Ansuzalgiz/Falcon/Images/Flywheels1.jpg

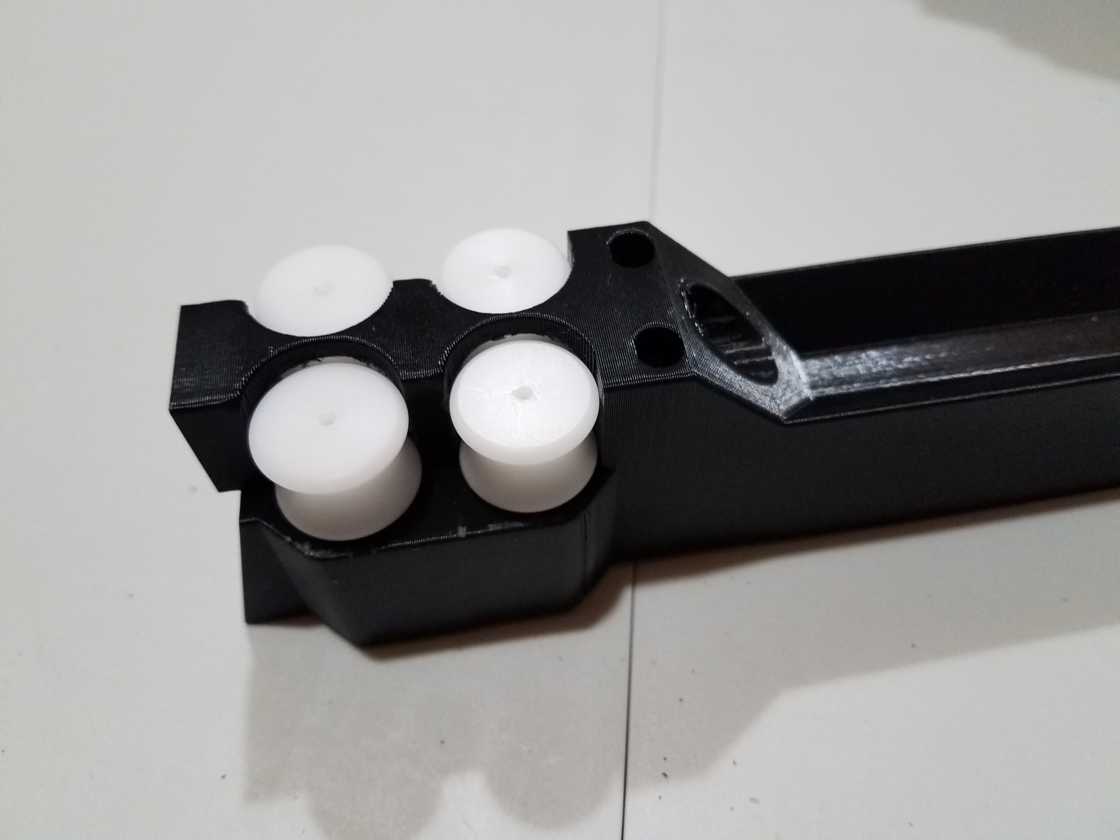
Images/Flywheels1.jpg
