Ansuzalgiz/Falcon/Images/HOLDsterCover.jpg

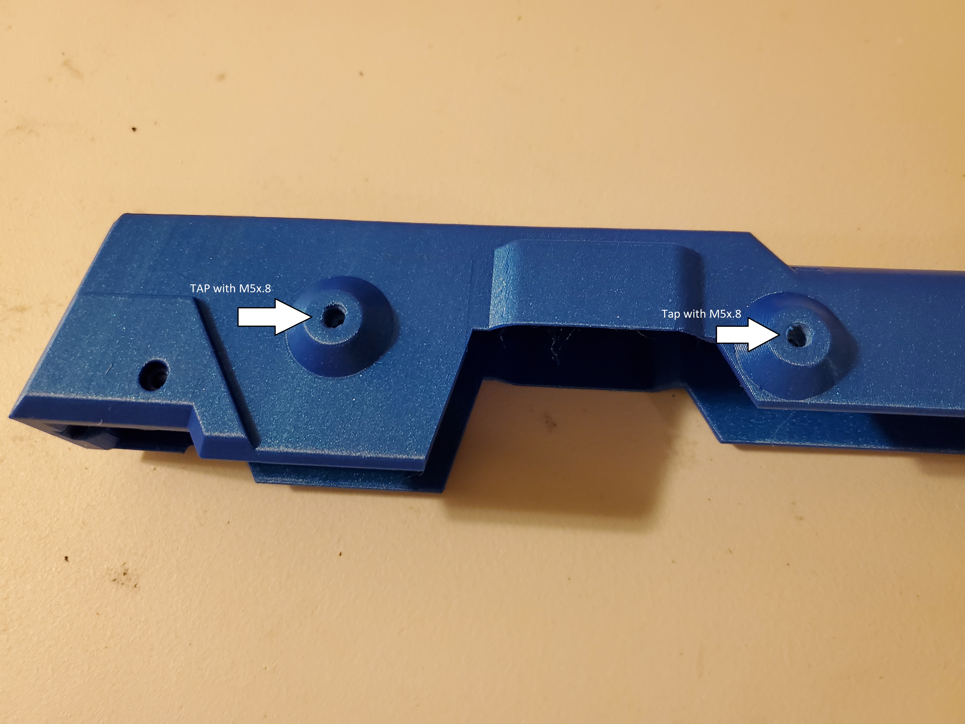
Images/HOLDsterCover.jpg
