Ansuzalgiz/Falcon/Images/HOLDsterFinished.jpg

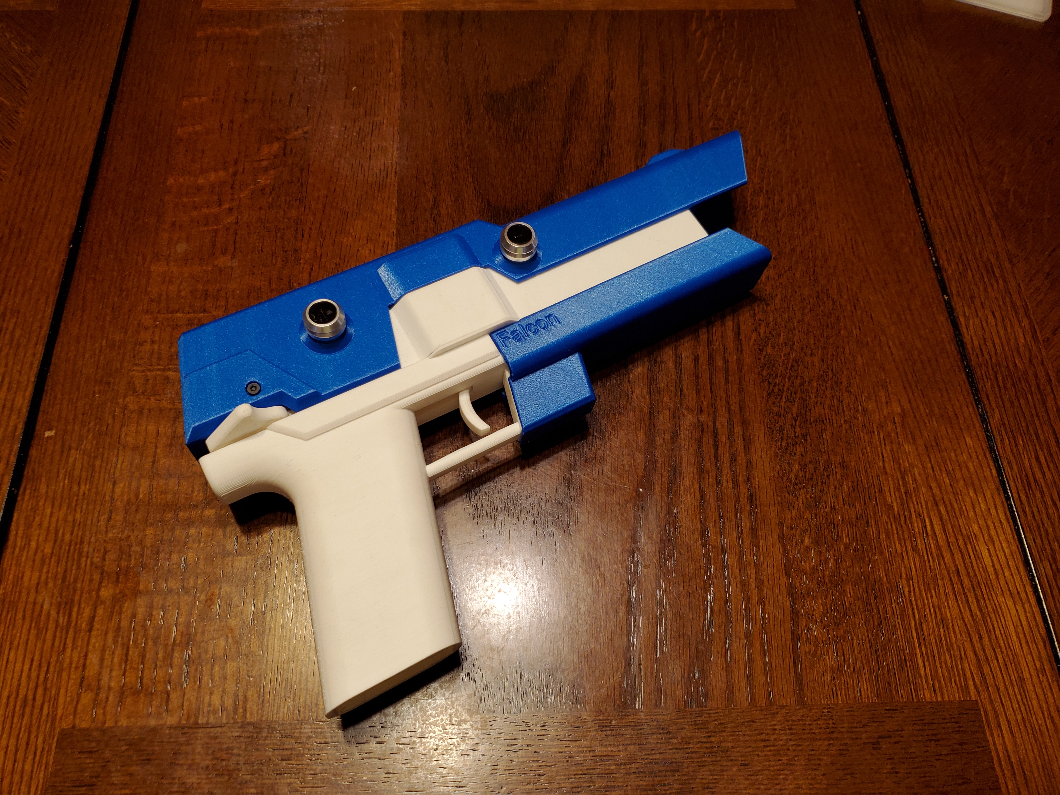
Images/HOLDsterFinished.jpg
