Ansuzalgiz/Falcon/Images/Insert1.jpg

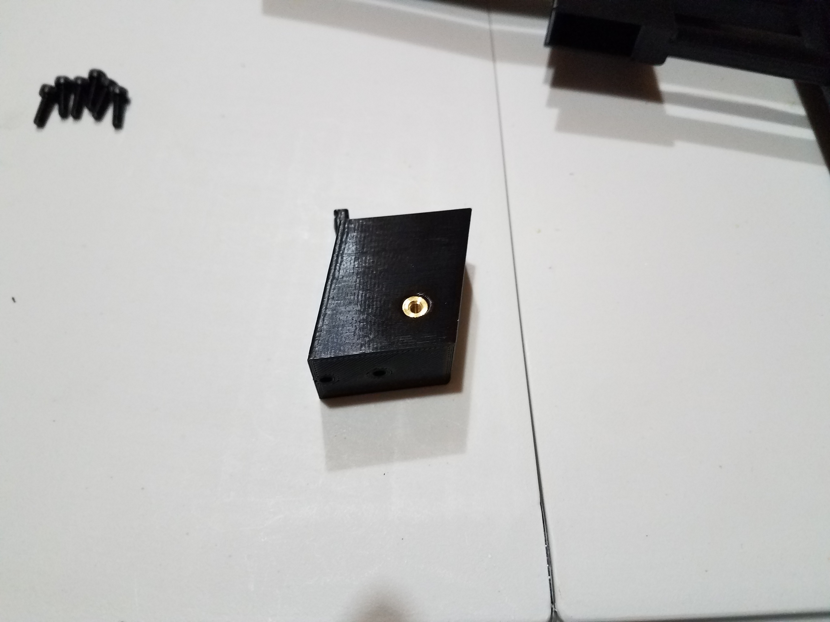
Images/Insert1.jpg
