Ansuzalgiz/Falcon/Images/Insert2.jpg

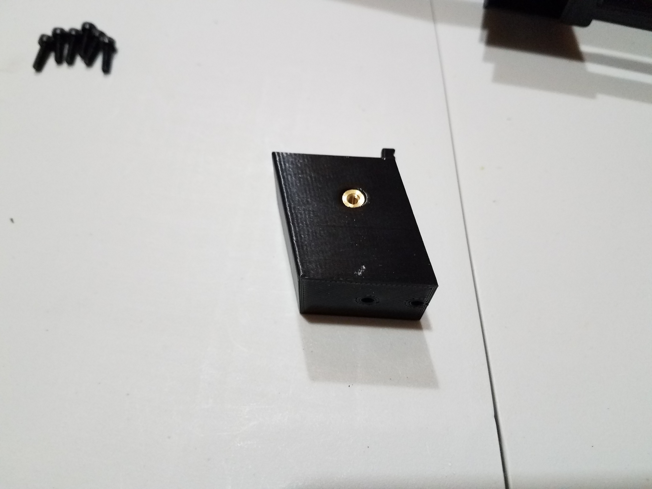
Images/Insert2.jpg
