Ansuzalgiz/Falcon/Images/Insert3.jpg

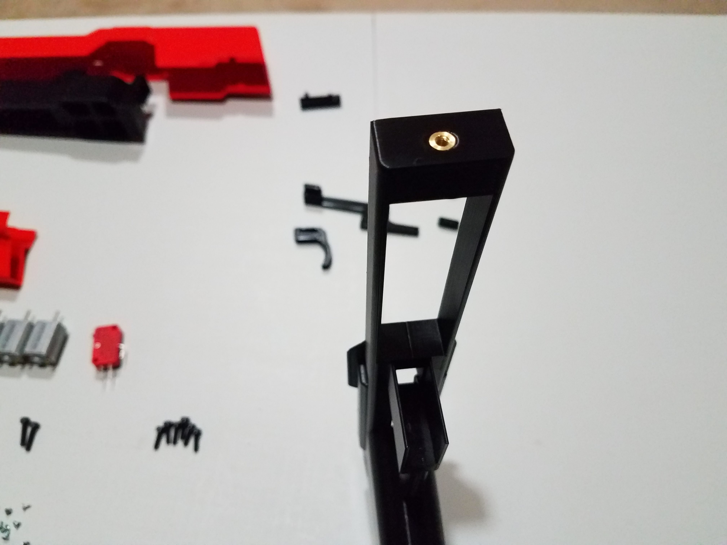
Images/Insert3.jpg
