Ansuzalgiz/Falcon/Images/Insert4.jpg

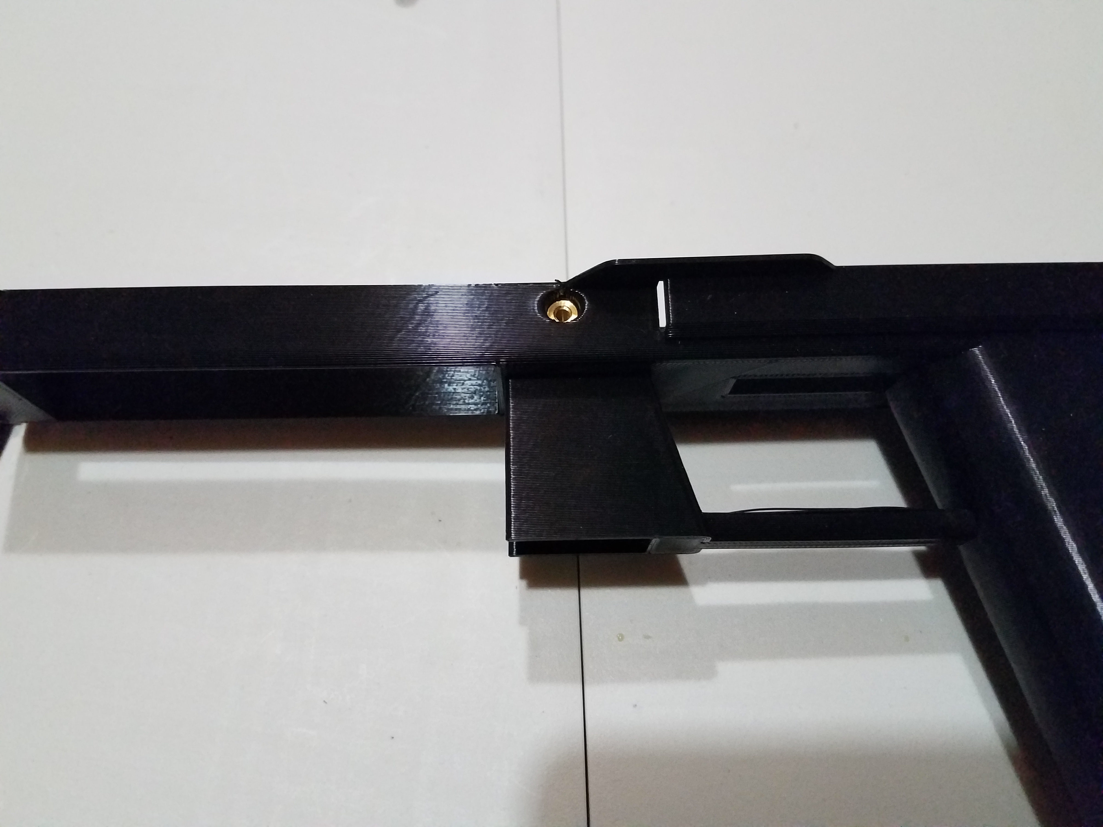
Images/Insert4.jpg
