Ansuzalgiz/Falcon/Images/Insert5.jpg

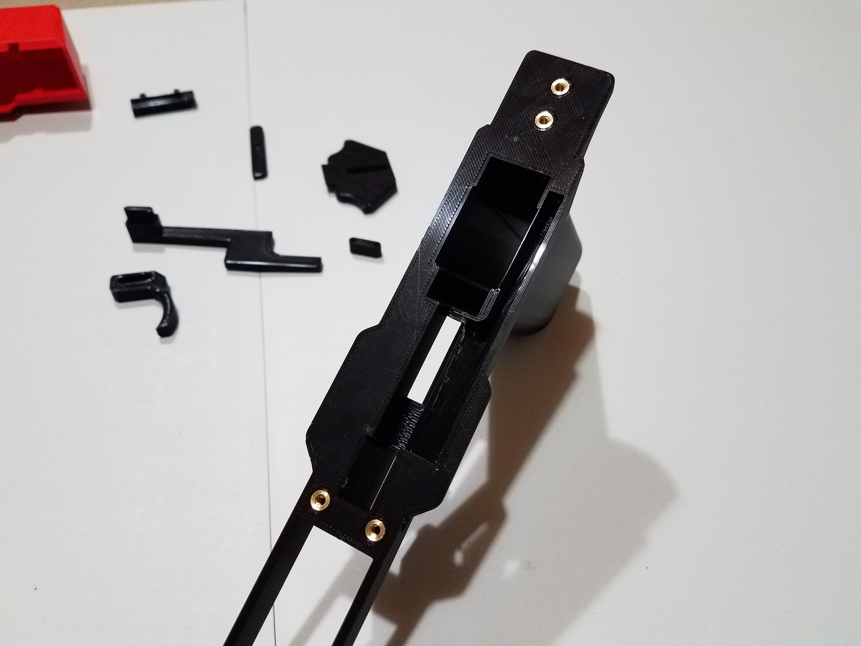
Images/Insert5.jpg
