Ansuzalgiz/Falcon/Images/MagRelease1.jpg

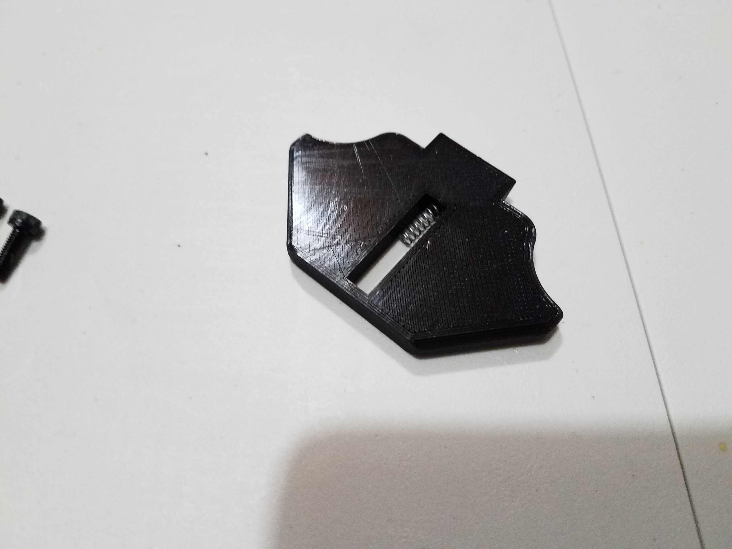
Images/MagRelease1.jpg
