Ansuzalgiz/Falcon/Images/MagRelease2.jpg

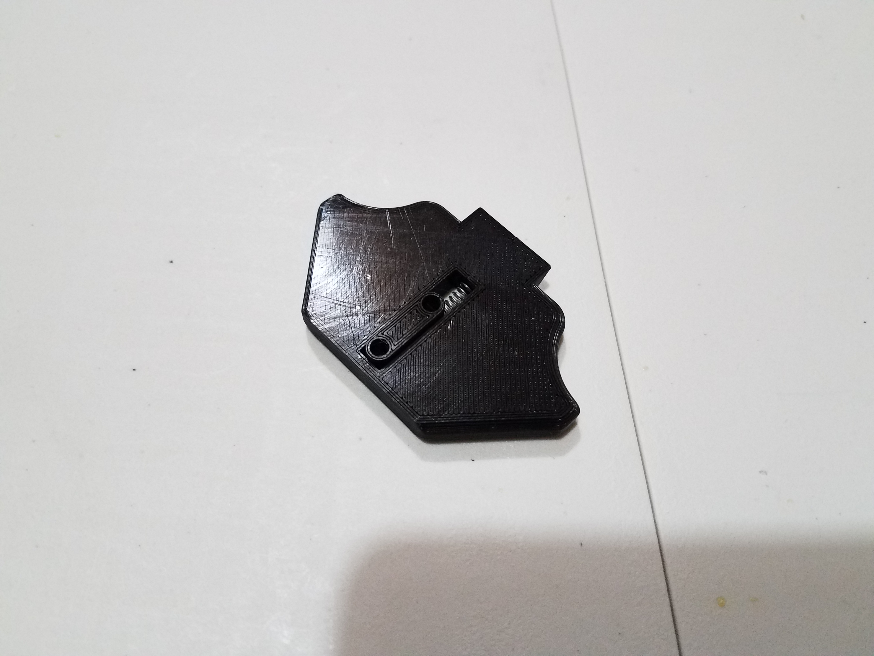
Images/MagRelease2.jpg
