Ansuzalgiz/Falcon/Images/MagRelease3.jpg

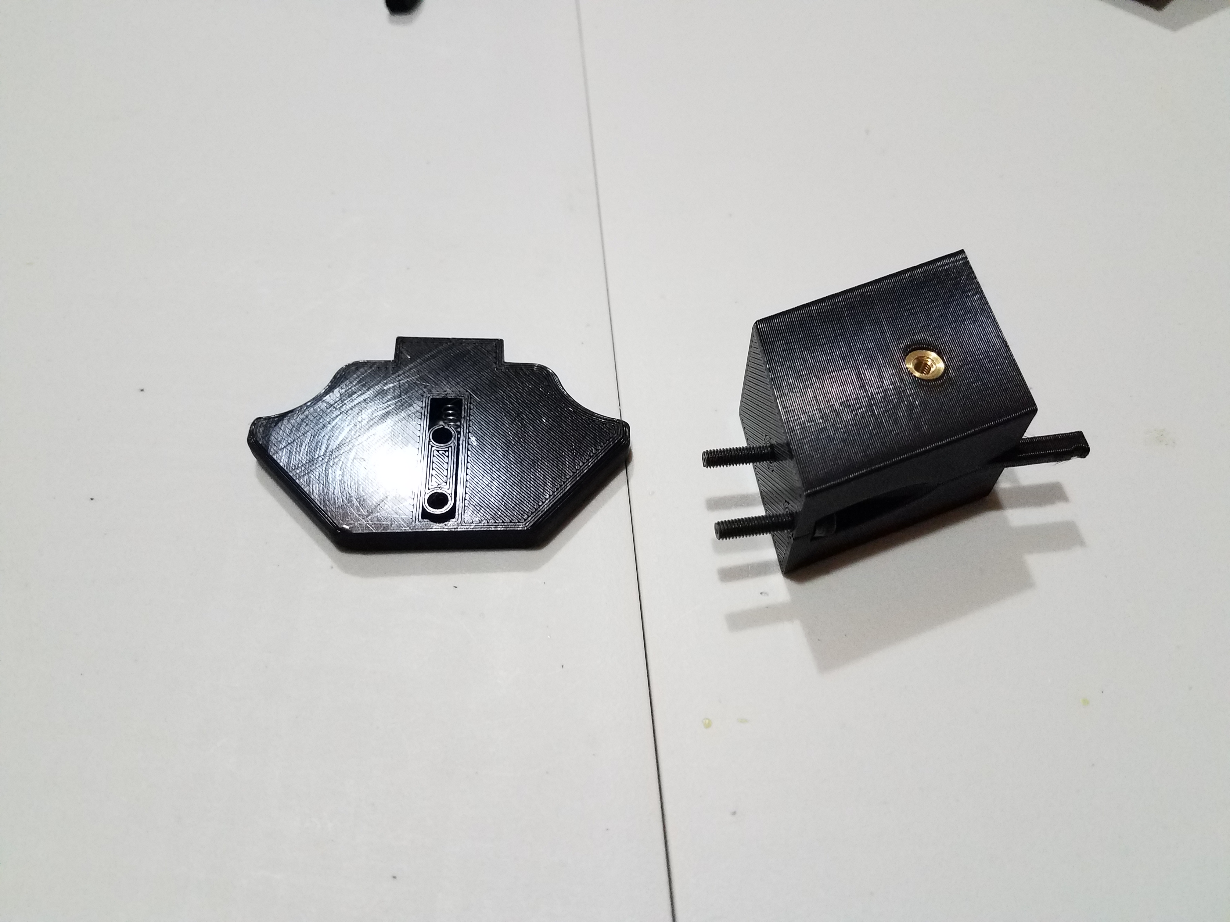
Images/MagRelease3.jpg
