Ansuzalgiz/Falcon/Images/MagRelease4.jpg

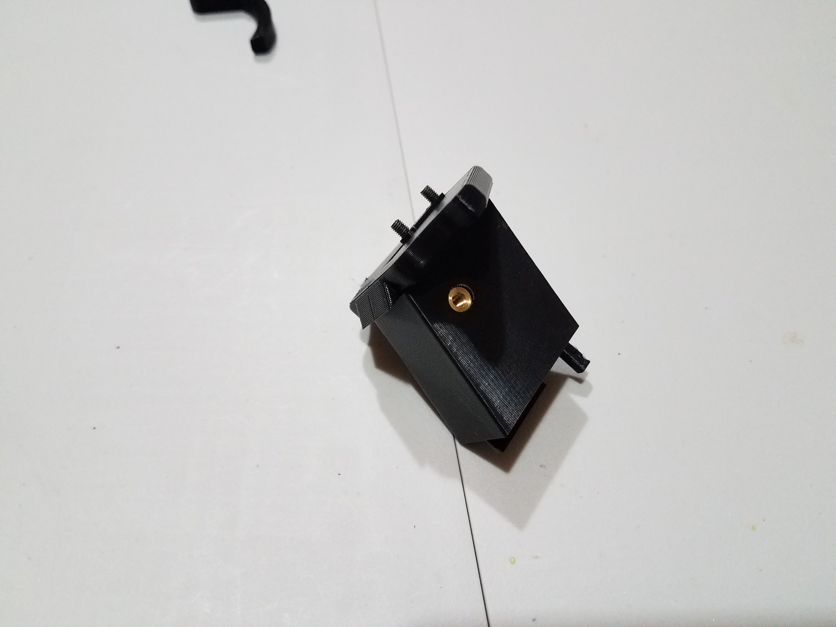
Images/MagRelease4.jpg
