Ansuzalgiz/Falcon/Images/MagRelease5.jpg

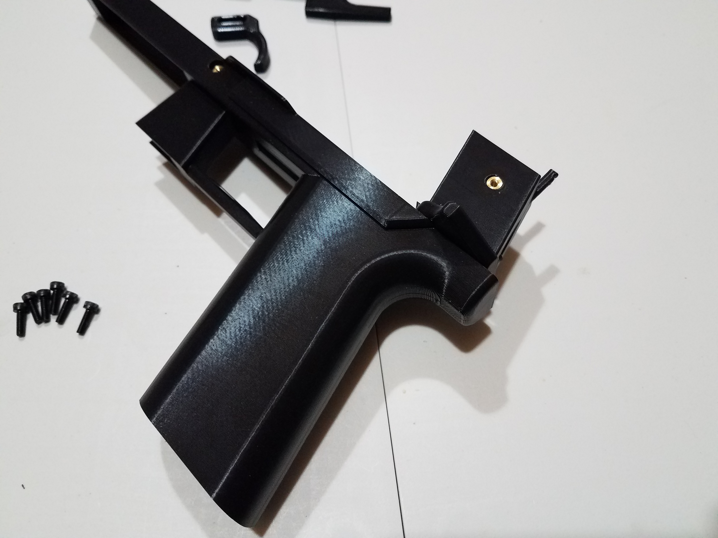
Images/MagRelease5.jpg
