Ansuzalgiz/Falcon/Images/Pusher1.jpg

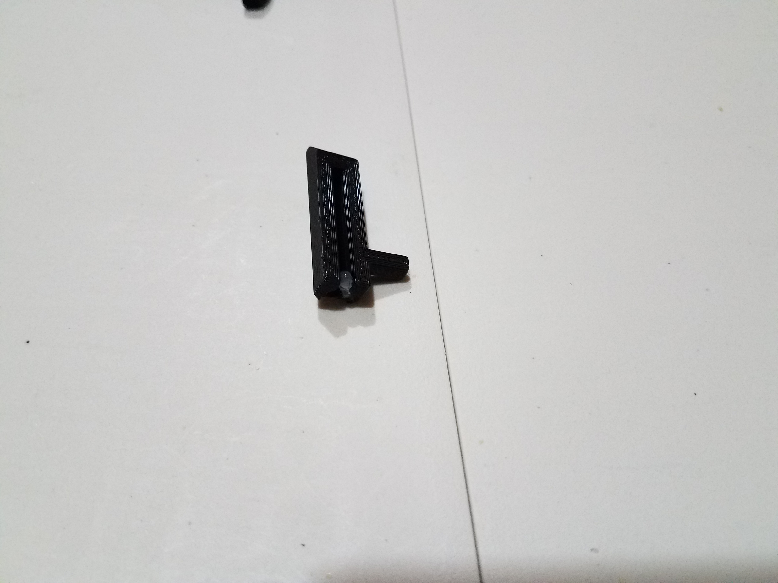
Images/Pusher1.jpg
