Ansuzalgiz/Falcon/Images/Switch1.jpg

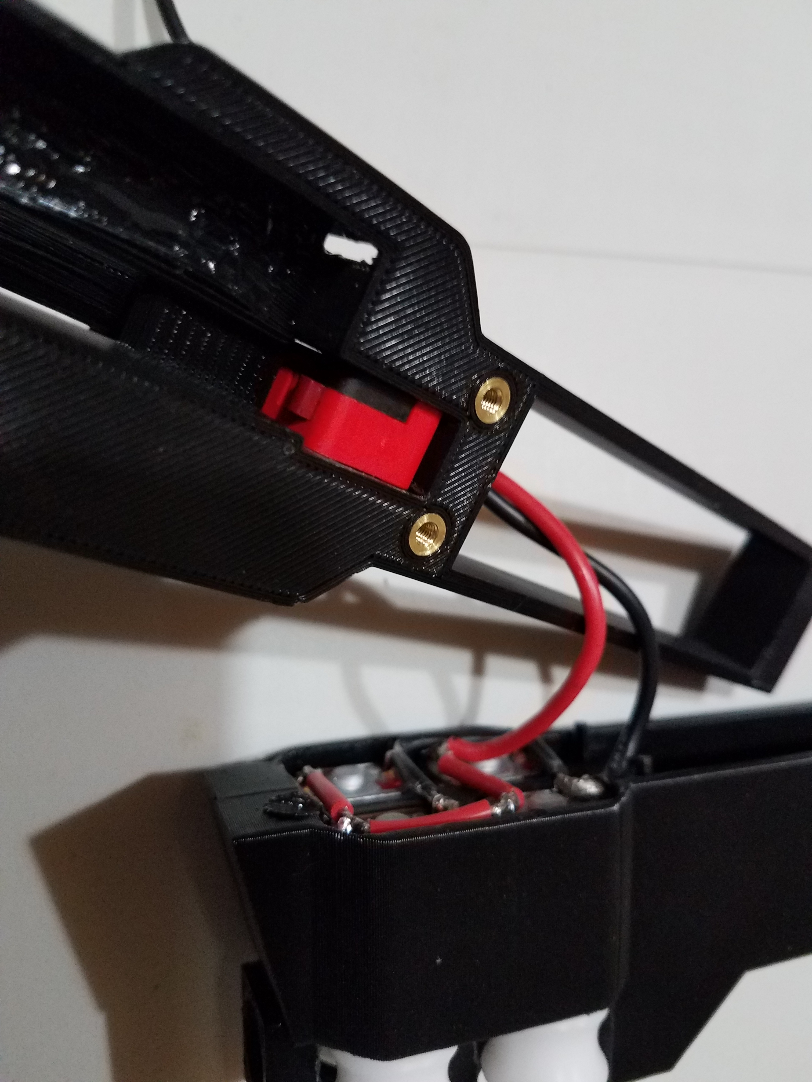
Images/Switch1.jpg
