Ansuzalgiz/Falcon/Images/Trigger1.jpg

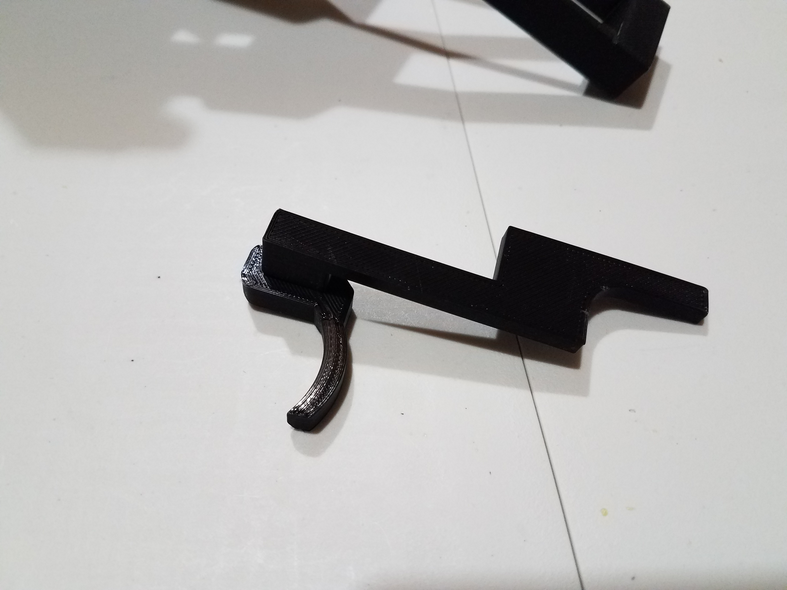
Images/Trigger1.jpg
