Ansuzalgiz/Falcon/Images/Trigger2.jpg

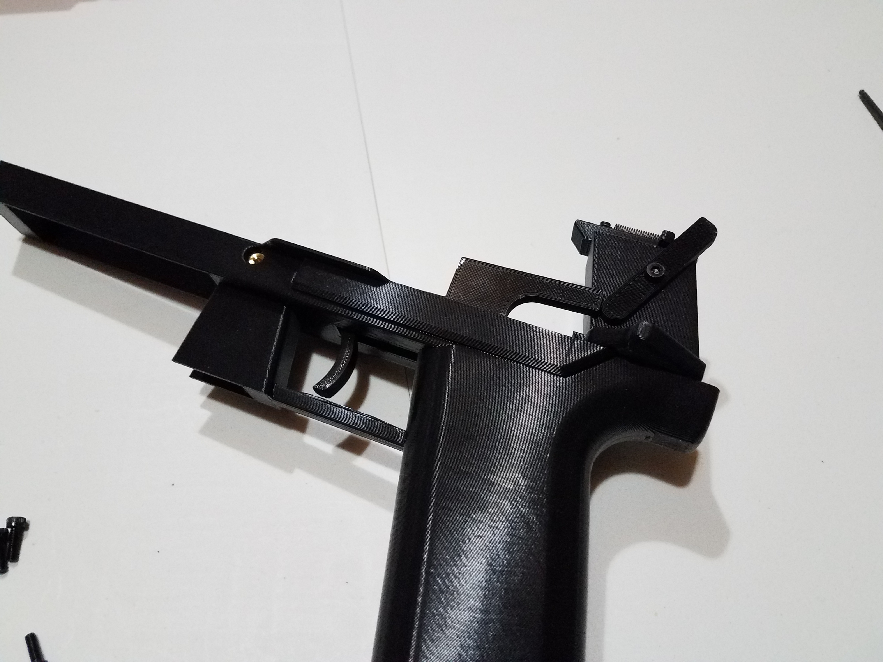
Images/Trigger2.jpg
