Ansuzalgiz/Falcon/Images/KitParts.jpg

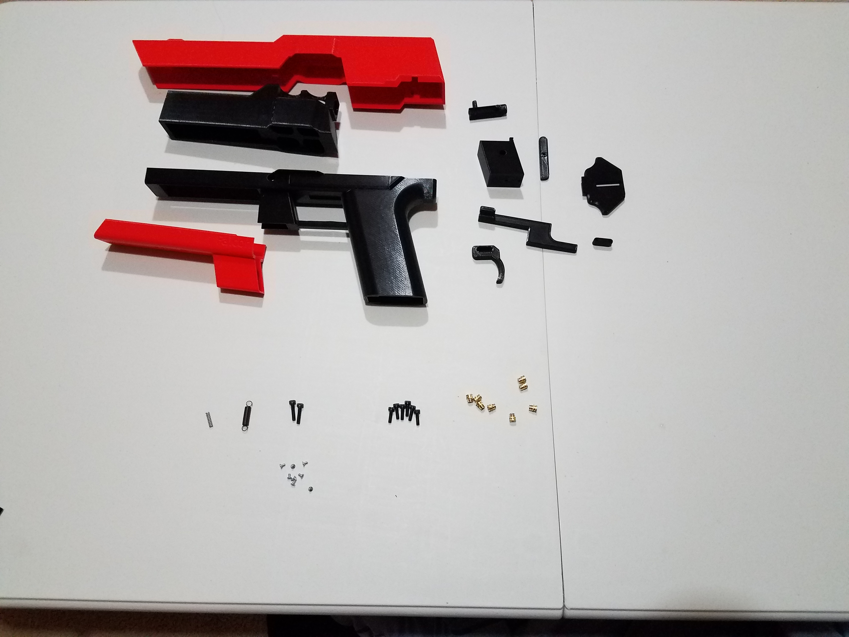
Images/KitParts.jpg
