Ansuzalgiz/Falcon/STLs/BatteryCover.stl

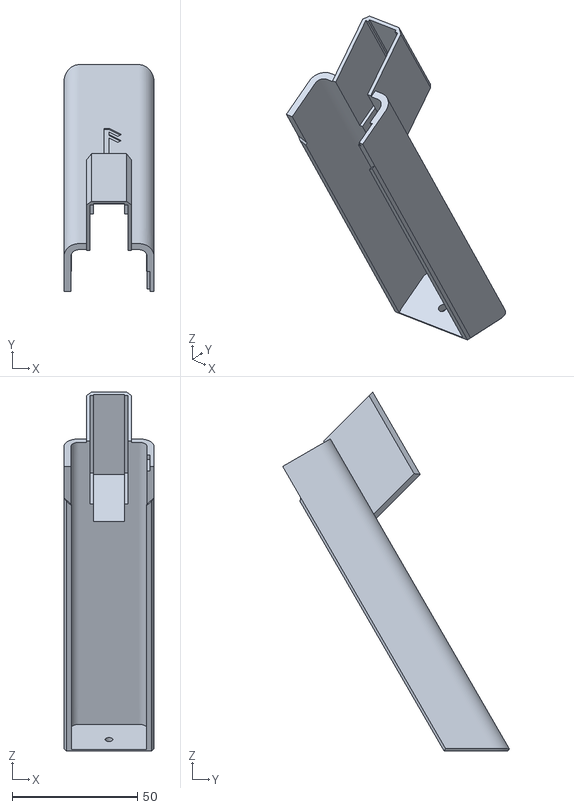
[picture p39: CAD file, 2020-02-27]
STLs/BatteryCover.stl
36.0 x 90.5 x 143.3
