Ansuzalgiz/Falcon/STLs/FlaredMagwell.stl

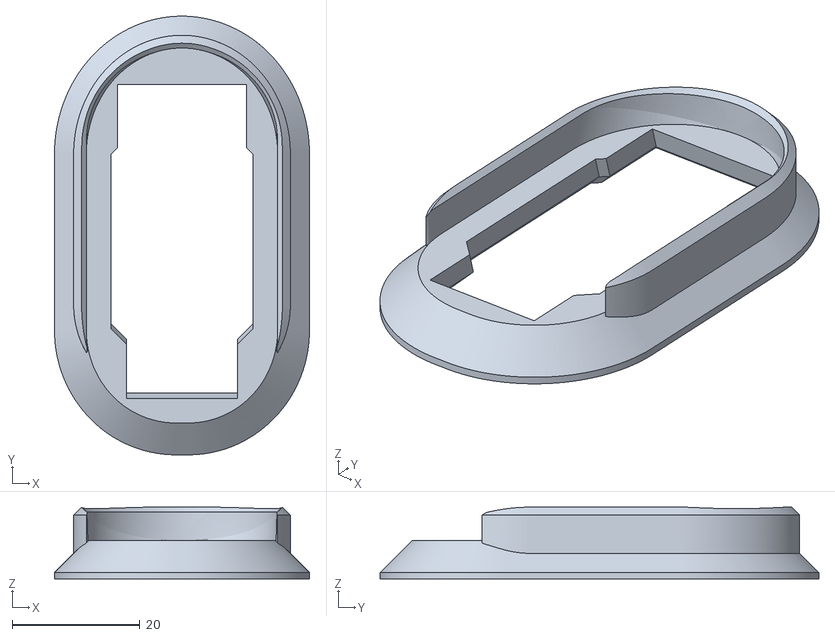
[picture p40: CAD file, 2020-02-27]
STLs/FlaredMagwell.stl
40.0 x 68.8 x 11.3
