Ansuzalgiz/Falcon/STLs/PusherMount.stl

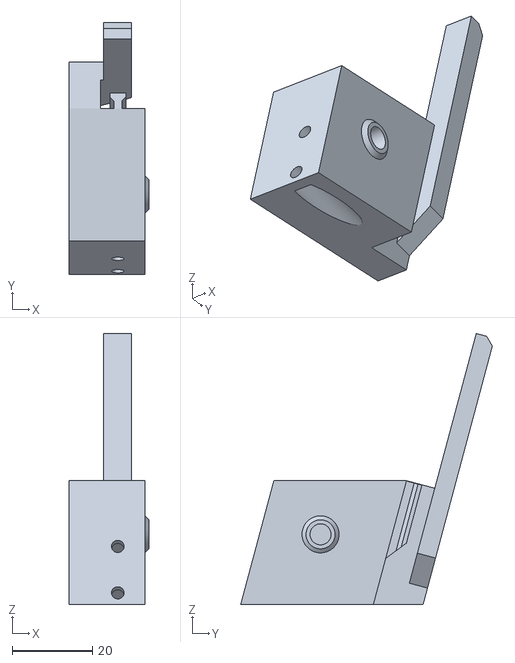
[picture p41: CAD file, 2020-02-27]
STLs/PusherMount.stl
20.0 x 62.8 x 67.7
