Ansuzalgiz/Falcon/Images/FinalAssembly1.jpg

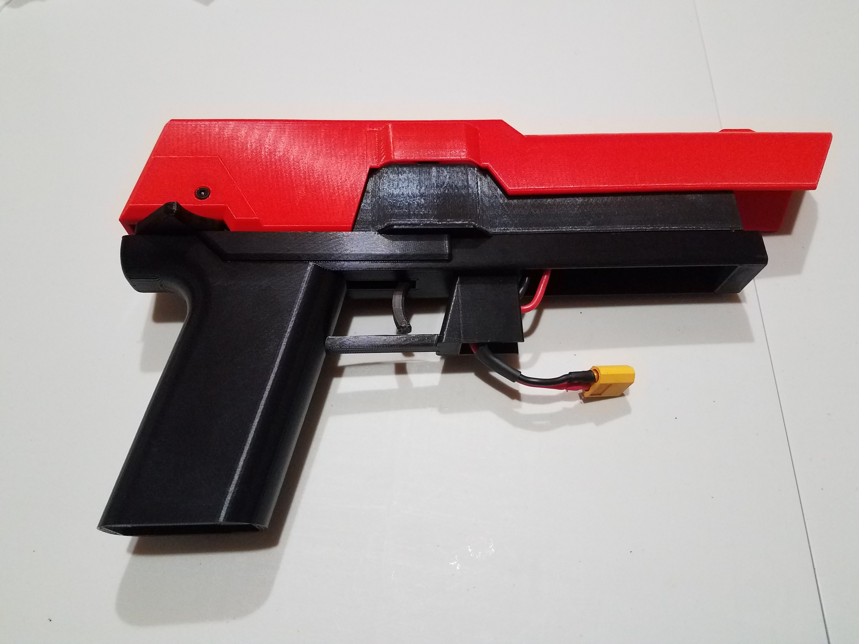
Images/FinalAssembly1.jpg
