Ansuzalgiz/Falcon/Images/FinalAssembly2.jpg

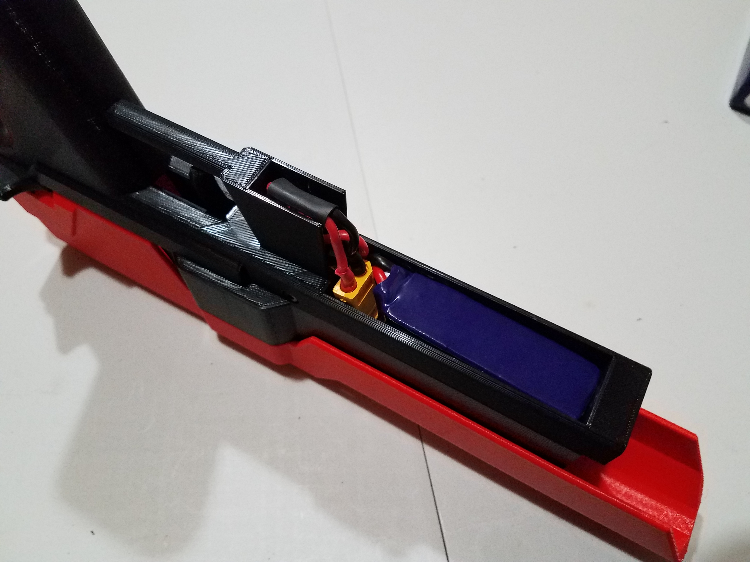
Images/FinalAssembly2.jpg
