Ansuzalgiz/Falcon/Images/FinalAssembly3.jpg

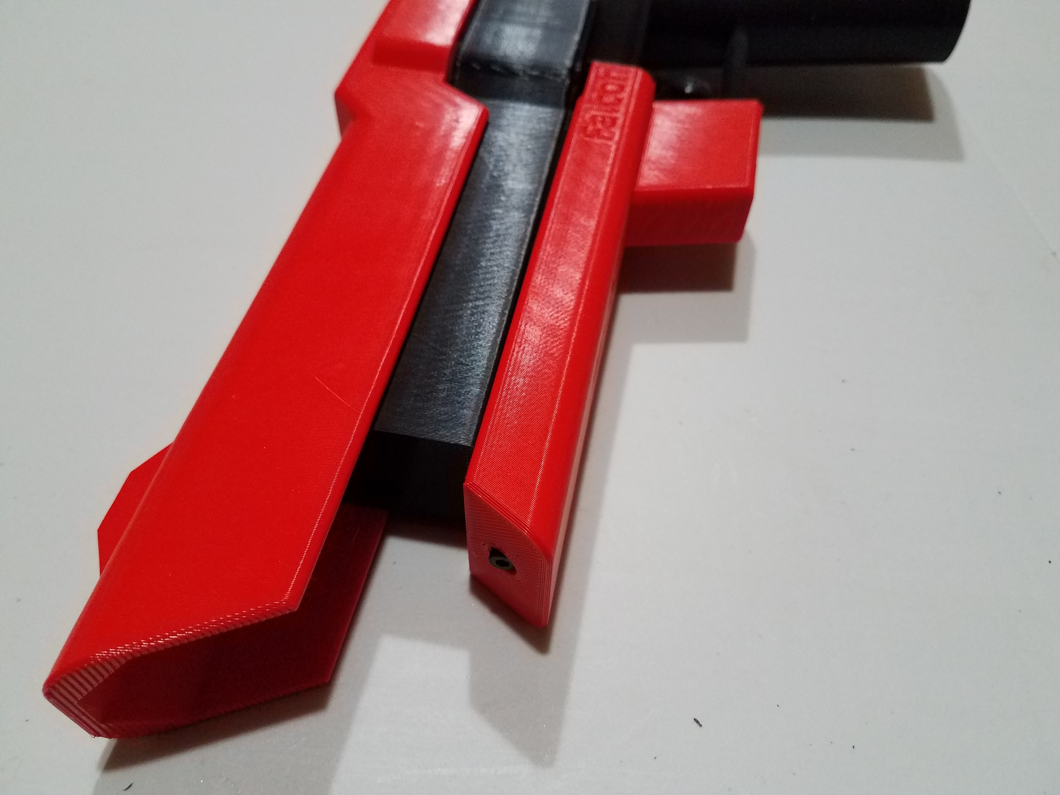
Images/FinalAssembly3.jpg
