Ansuzalgiz/Falcon/Images/Wiring2.jpg

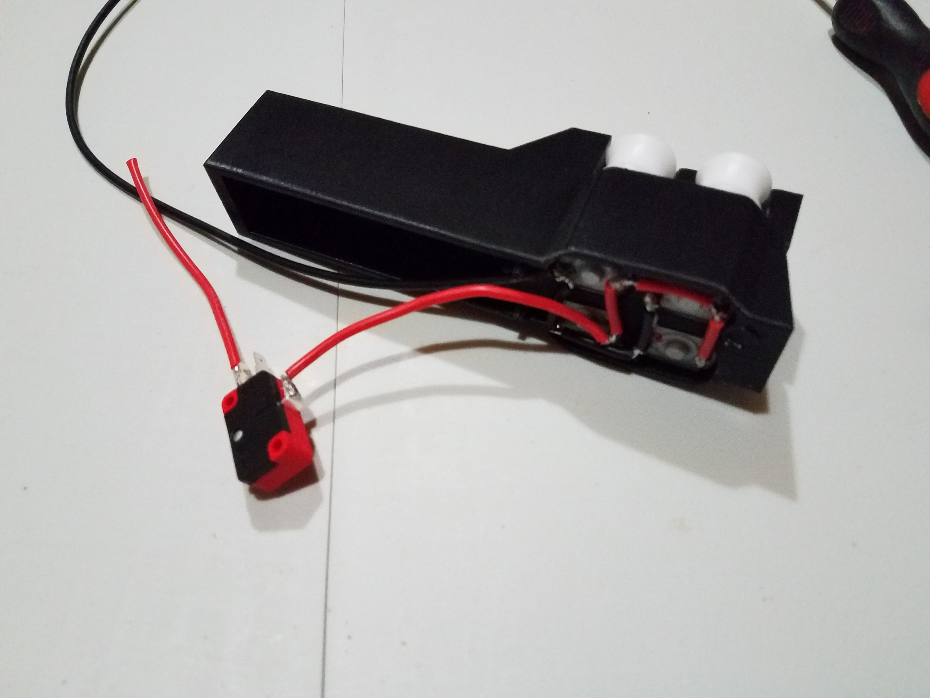
Images/Wiring2.jpg
