Ansuzalgiz/Falcon/Images/Wiring3.jpg

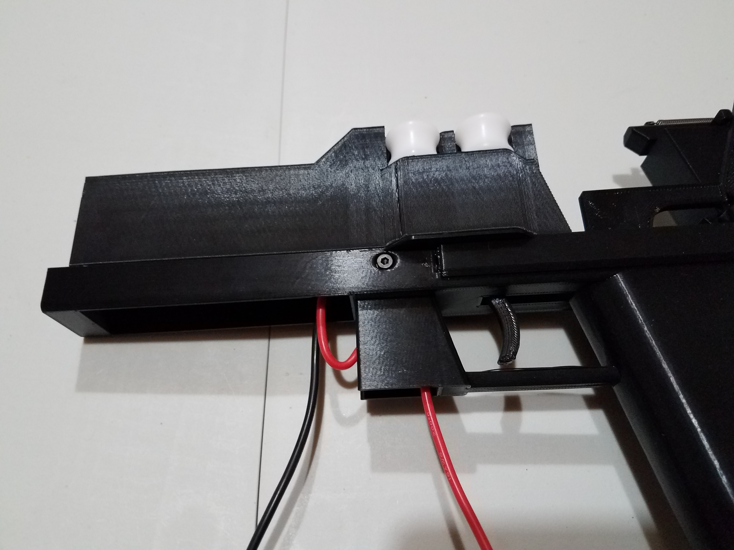
Images/Wiring3.jpg
