Ansuzalgiz/Falcon/Images/Wiring4.jpg

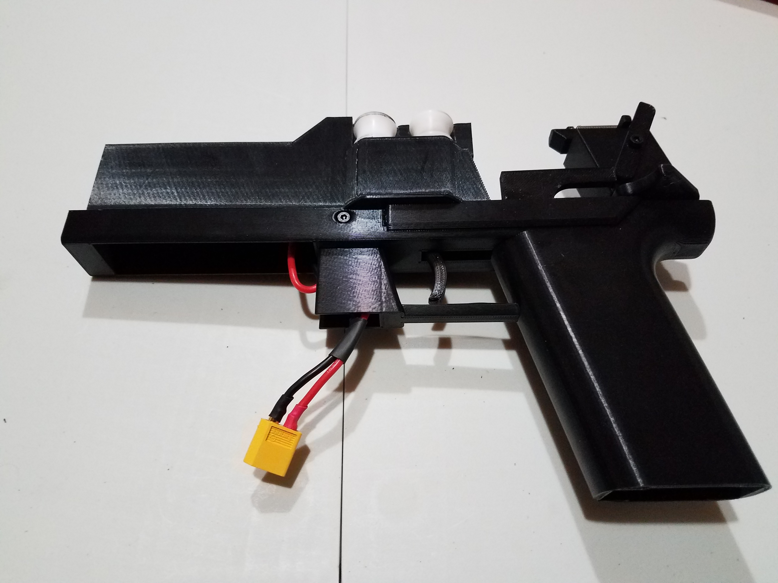
Images/Wiring4.jpg
